rubillos/RV-Bridge/images/box_wire.jpeg

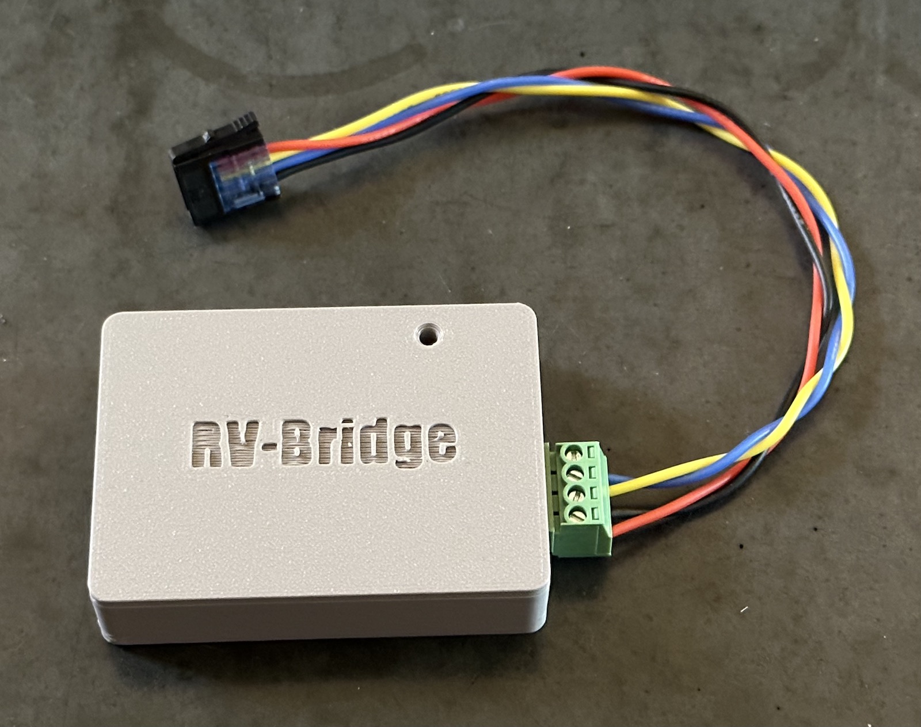
images/box_wire.jpeg
