rubillos/RV-Bridge/images/open_box_scale.jpeg

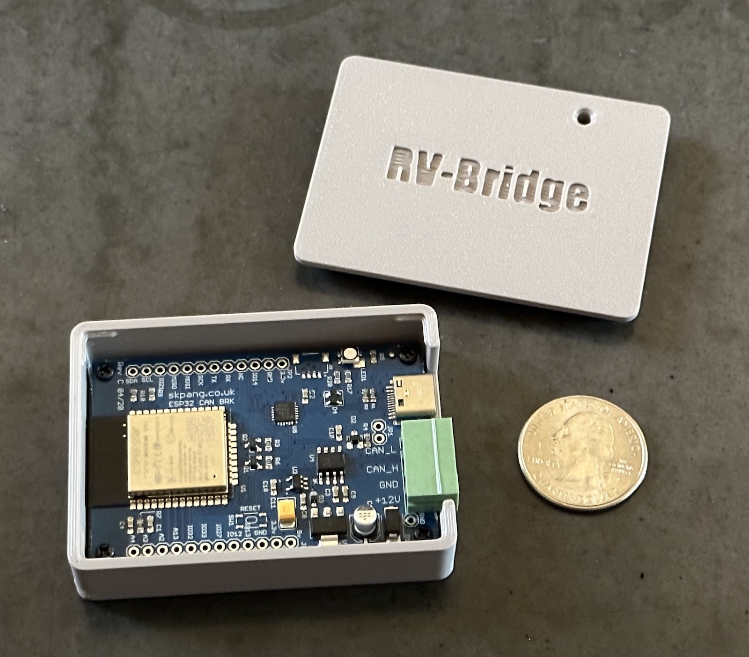
images/open_box_scale.jpeg
